Matthewsw1234/DJI-M600-SAR/Images/IMG_0261(2).JPG

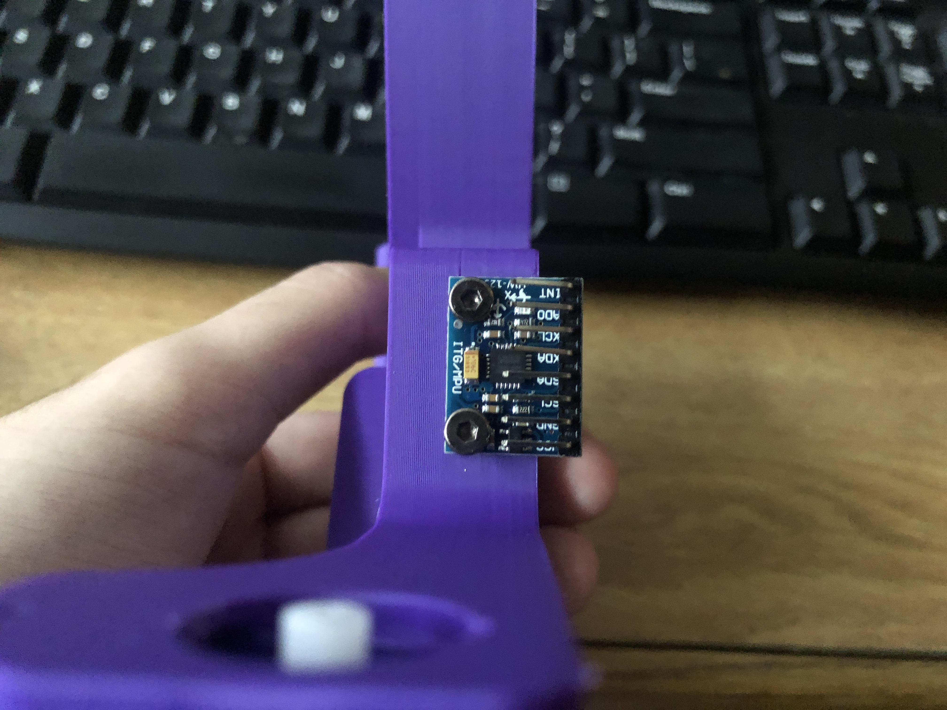
Images/IMG_0261(2).JPG
